romanhujer/SQM/Doc/Android KstartLite.png

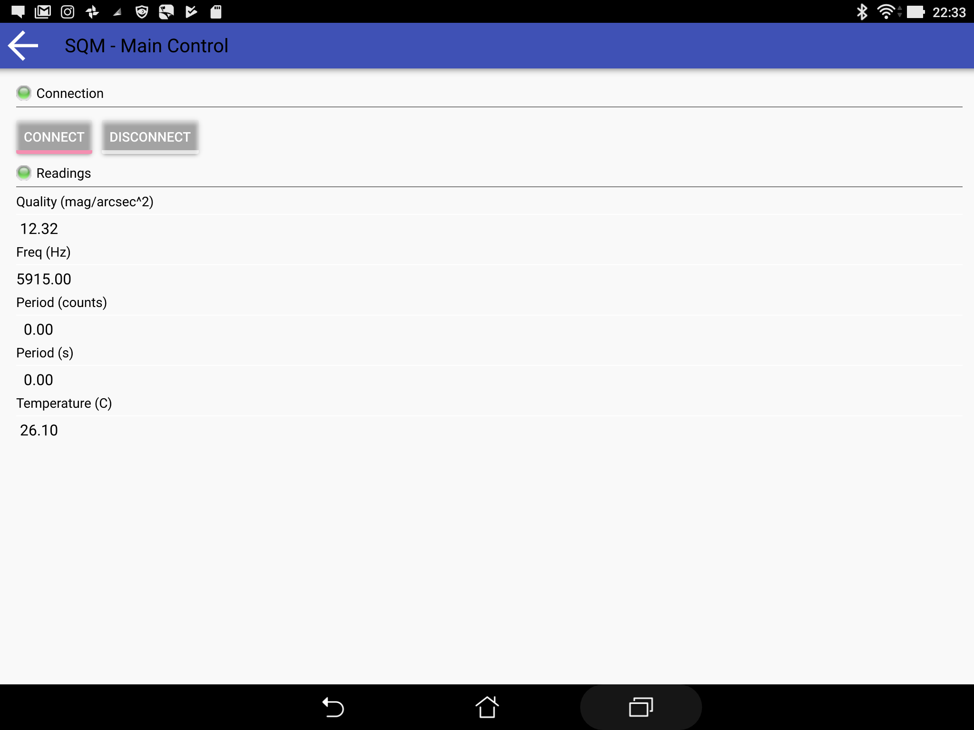
Doc/Android KstartLite.png
