romanhujer/SQM/Doc/Finall version.jpg

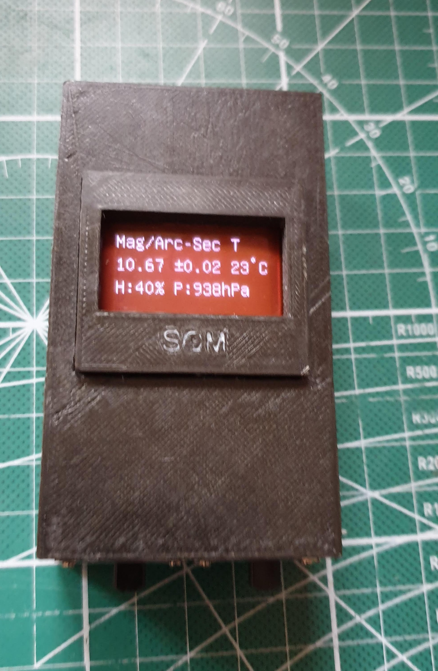
Doc/Finall version.jpg
