romanhujer/SQM/Doc/First prototrype.jpg

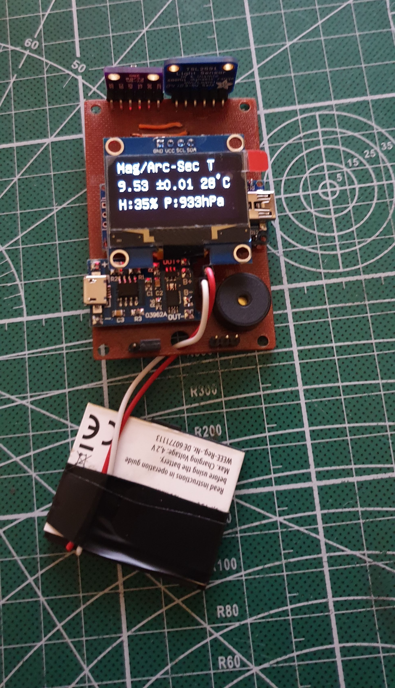
Doc/First prototrype.jpg
