romanhujer/SQM/Doc/Inastall battery.jpg

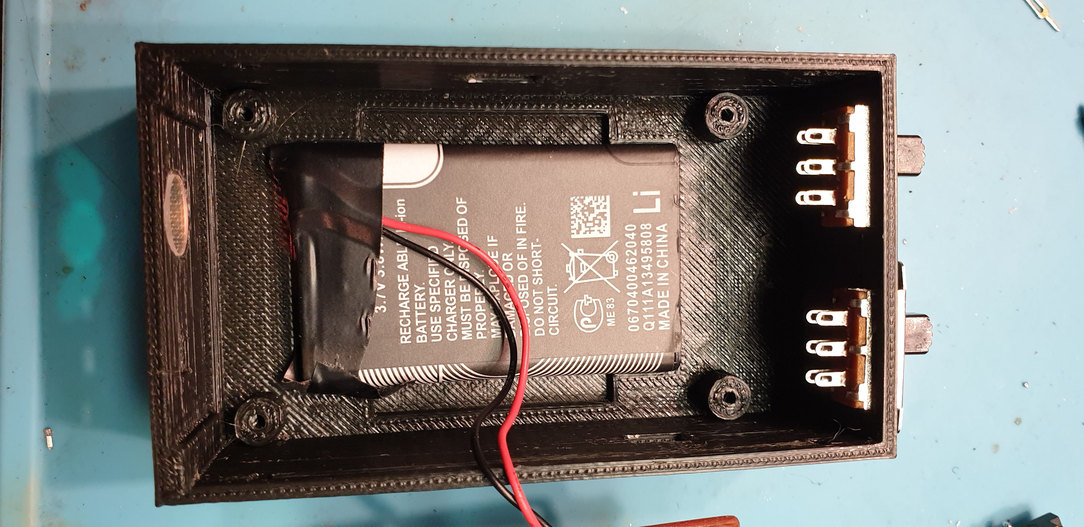
Doc/Inastall battery.jpg
