romanhujer/SQM/Doc/iOS  iINDI.PNG

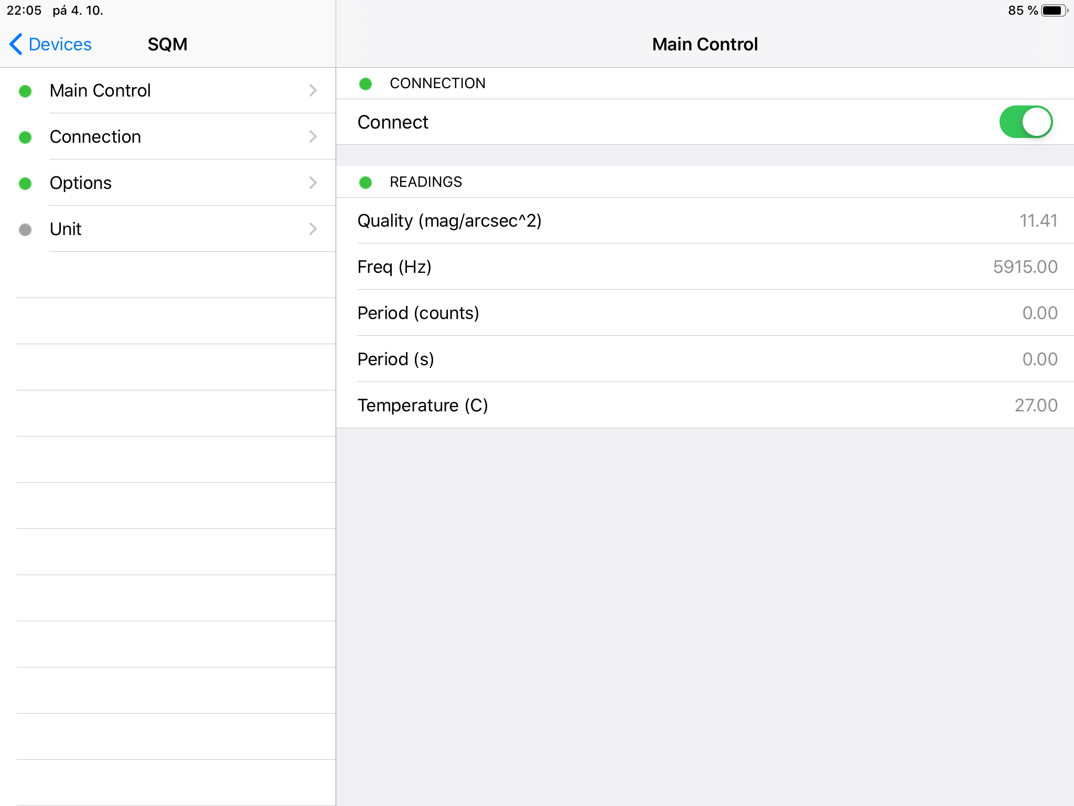
Doc/iOS iINDI.PNG
