romanhujer/SQM/Doc/JLCPCB  profi PCB V1.1b.jpg

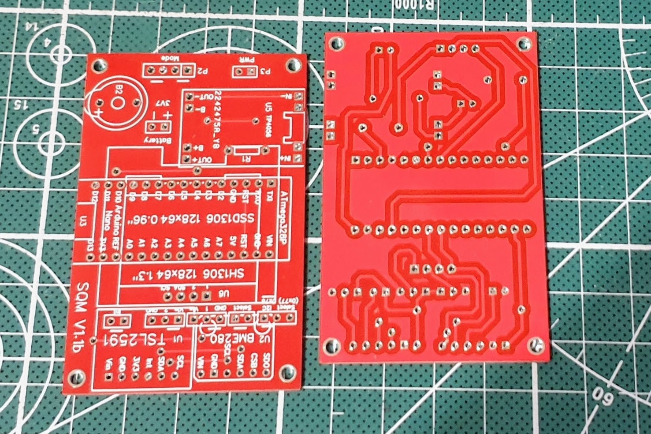
Doc/JLCPCB profi PCB V1.1b.jpg
