romanhujer/SQM/Doc/KStars.png

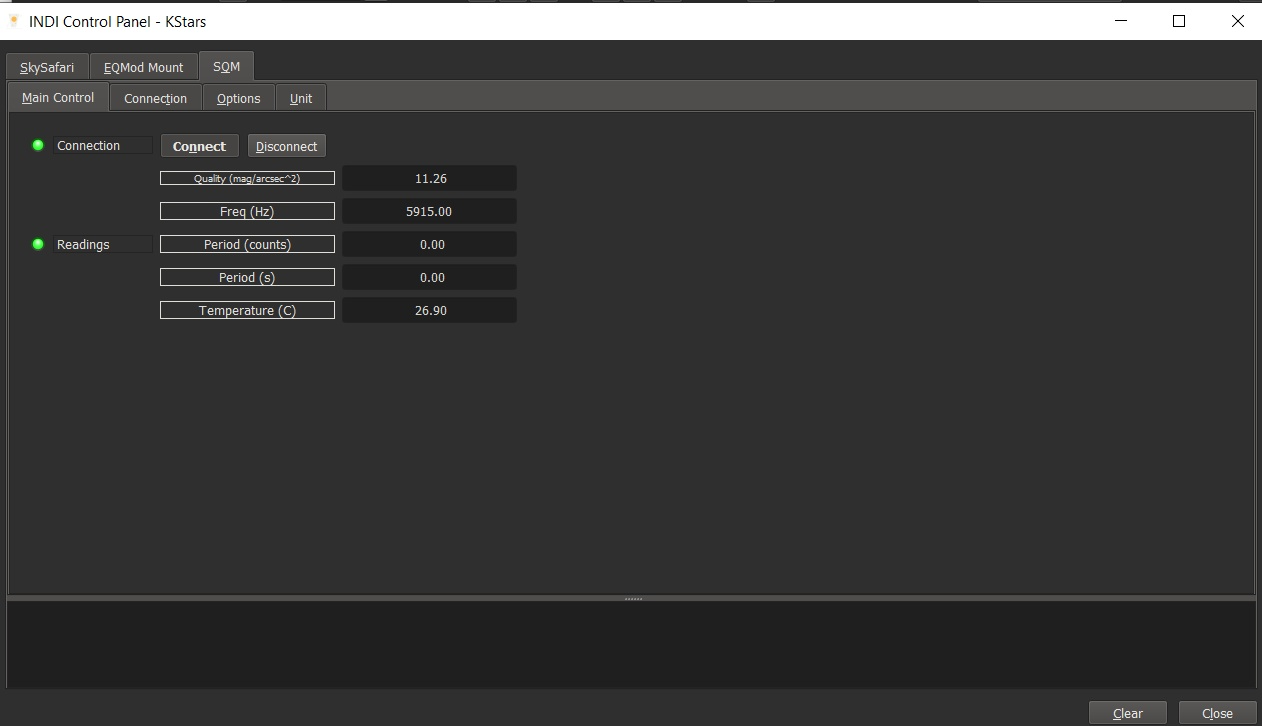
Doc/KStars.png
