romanhujer/SQM/Doc/SQM-in-APT.JPG

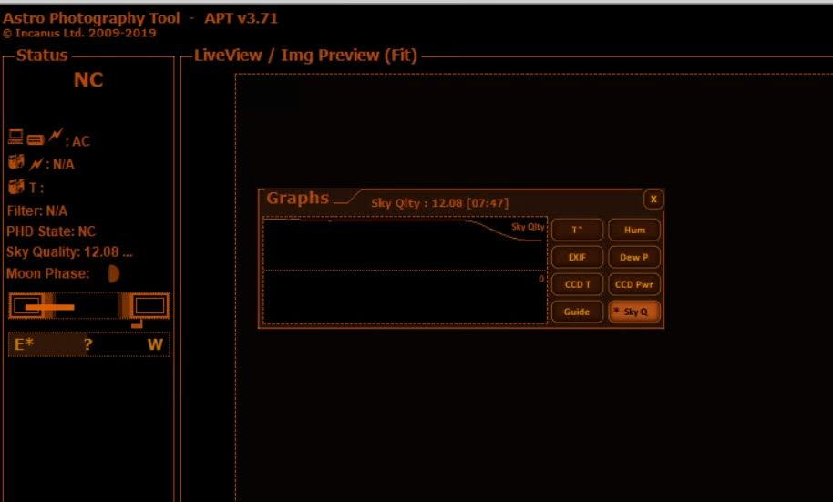
Doc/SQM-in-APT.JPG
