romanhujer/SQM/Doc/SQM.jpg

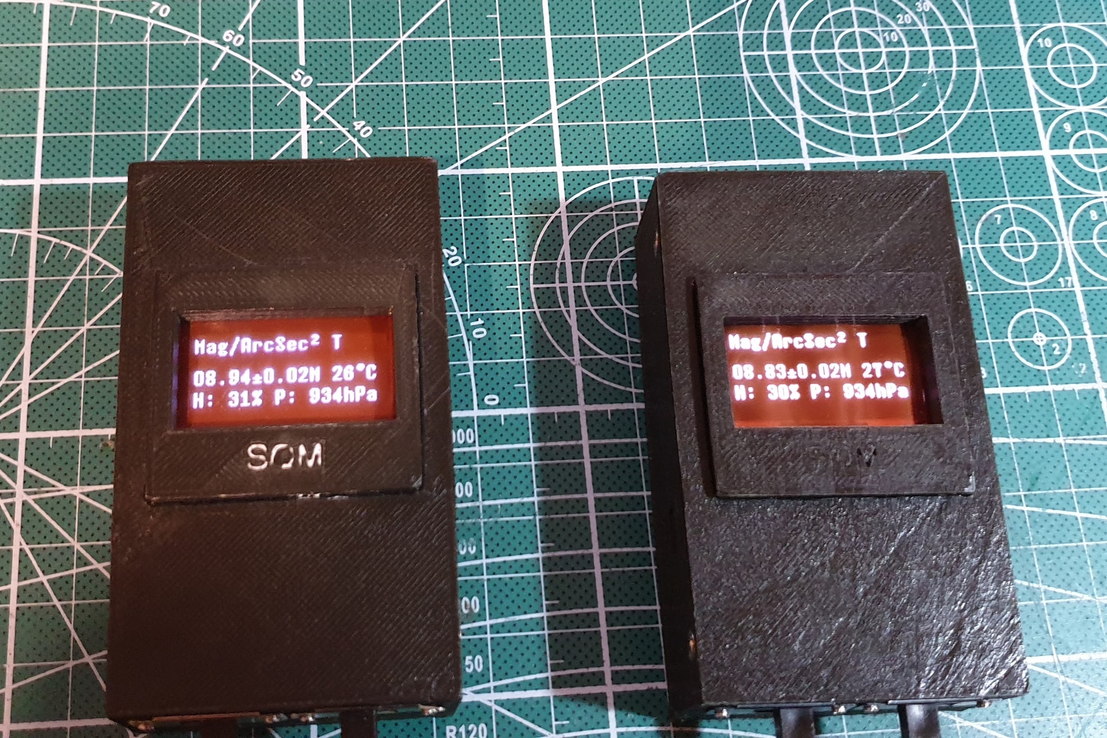
Doc/SQM.jpg
