romanhujer/SQM/Doc/UnihedromApp.JPG

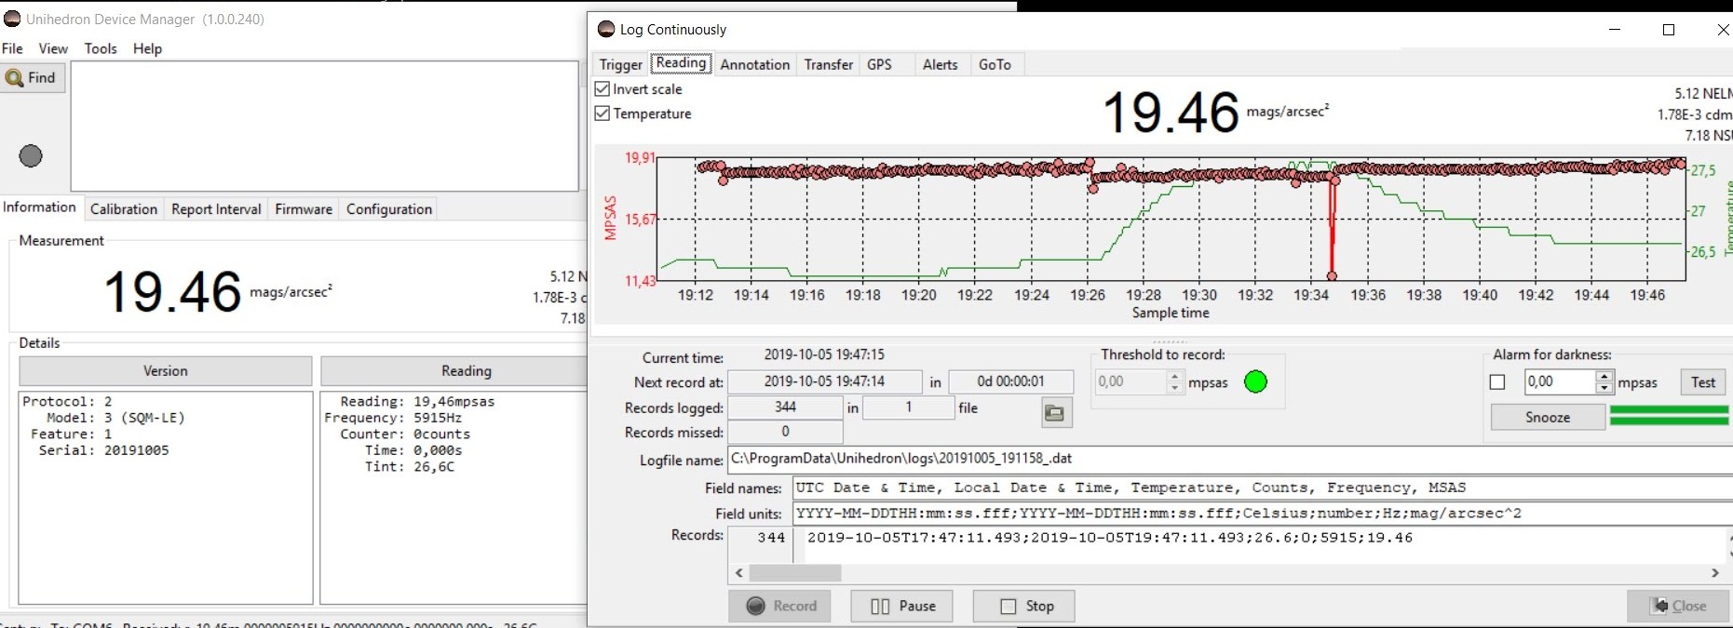
Doc/UnihedromApp.JPG
