romanhujer/SQM/Doc/WebManager BoxInfo.PNG

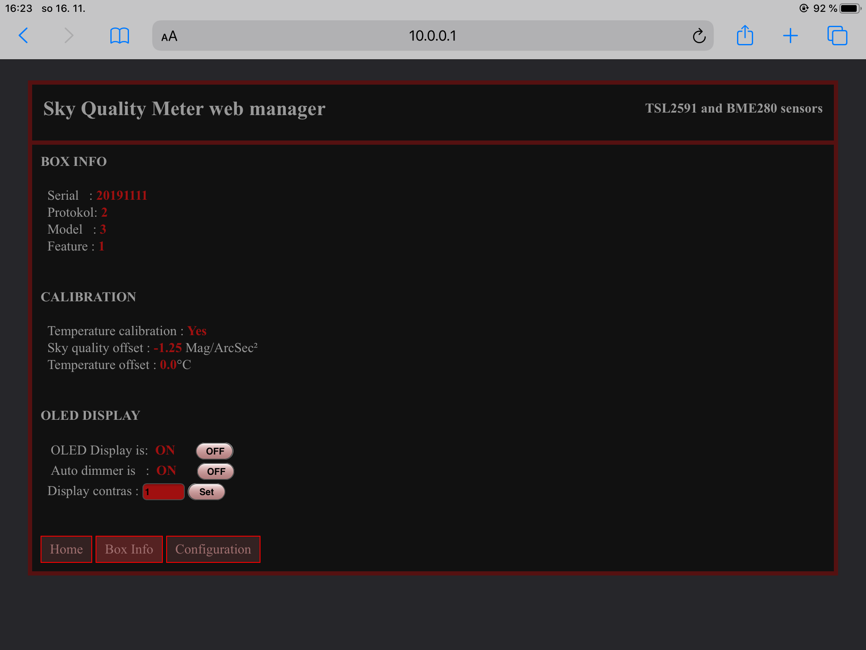
Doc/WebManager BoxInfo.PNG
