romanhujer/SQM/Doc/WebManager Config.PNG

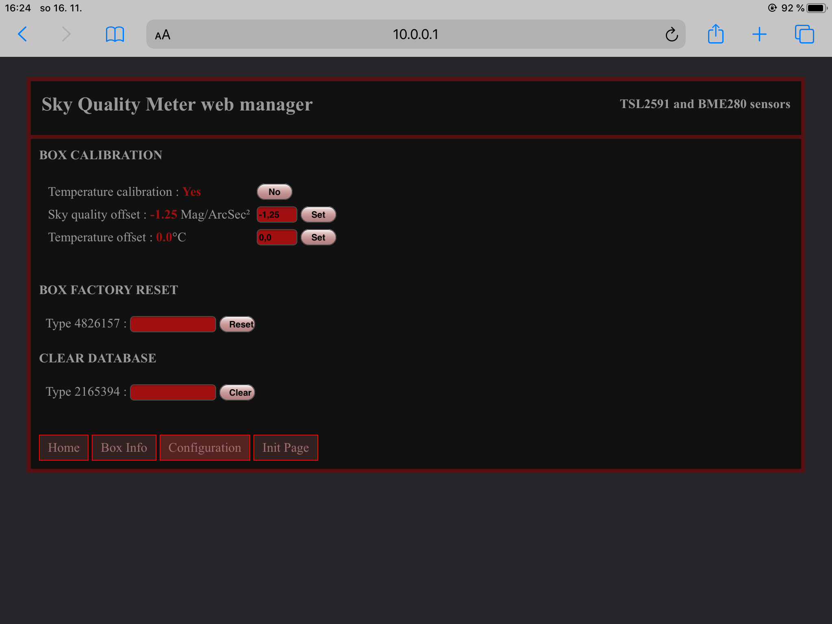
Doc/WebManager Config.PNG
