romanhujer/SQM/Doc/WebManager.PNG

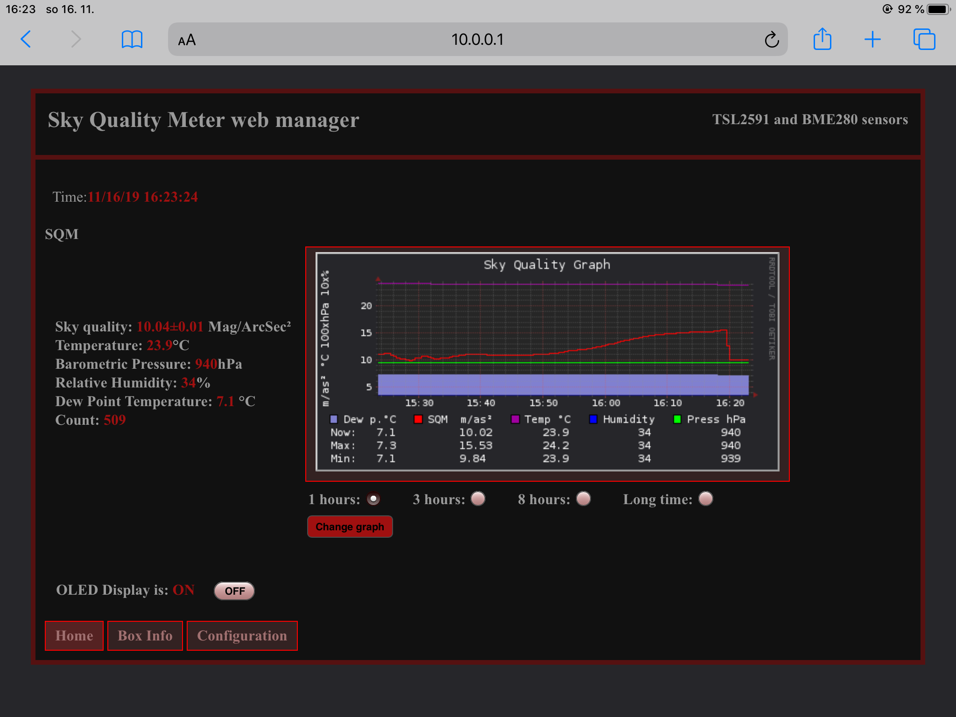
Doc/WebManager.PNG
