romanhujer/SQM/Doc/WebManagerGraphs.PNG

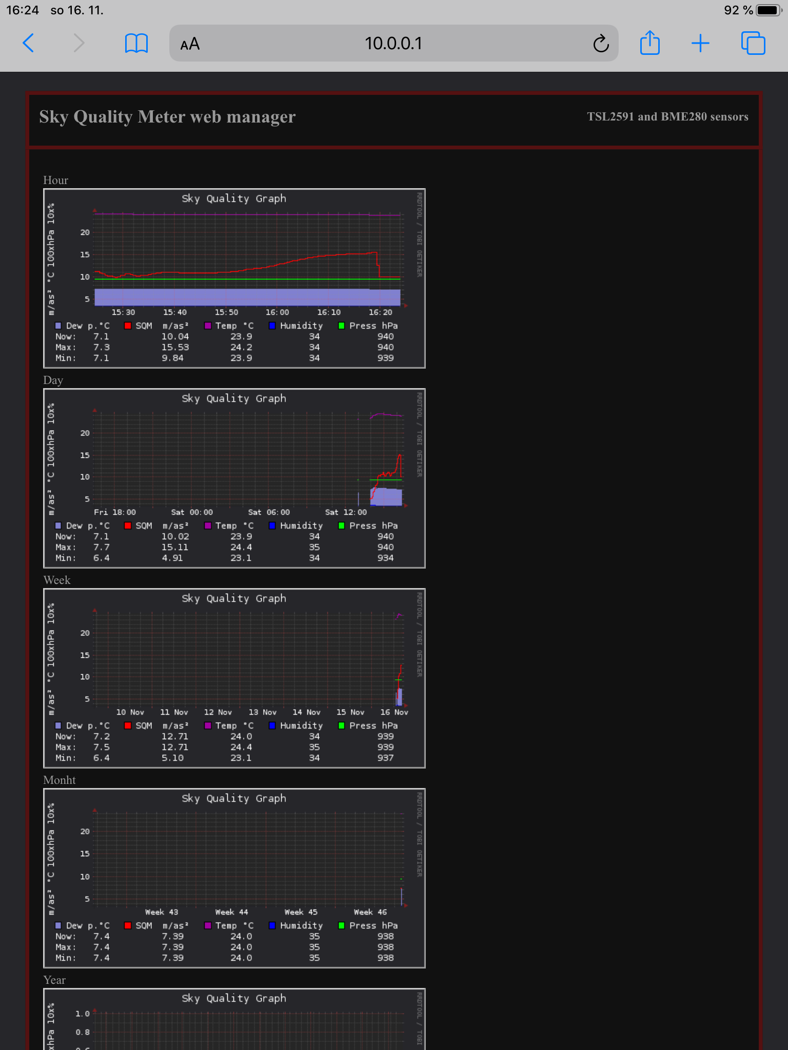
Doc/WebManagerGraphs.PNG
