romanhujer/SQM/sqm.png

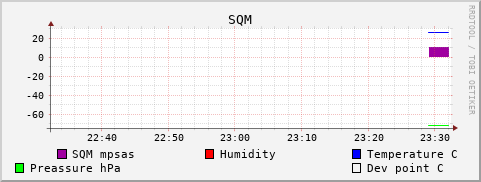
sqm.png
