romanhujer/SQM/sqmrrdweb/views/day.png

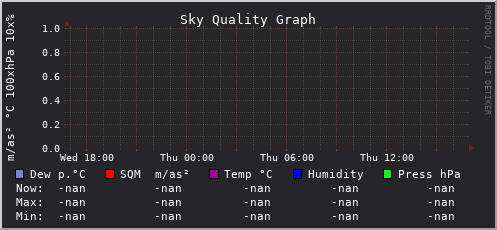
sqmrrdweb/views/day.png
