romanhujer/SQM/sqmrrdweb/views/monht.png

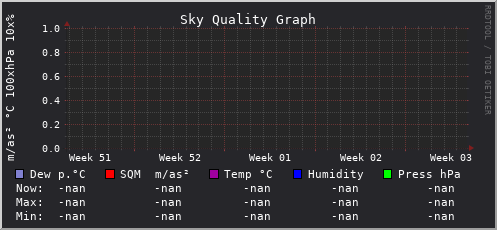
sqmrrdweb/views/monht.png
