romanhujer/SQM/sqmrrdweb/views/sqm.png

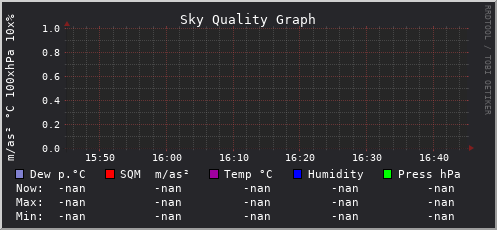
sqmrrdweb/views/sqm.png
