romanhujer/SQM/sqmrrdweb/views/week.png

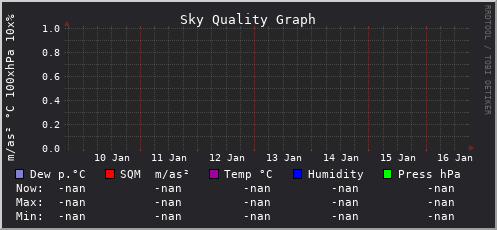
sqmrrdweb/views/week.png
