romanhujer/SQM/sqmrrdweb/views/year.png

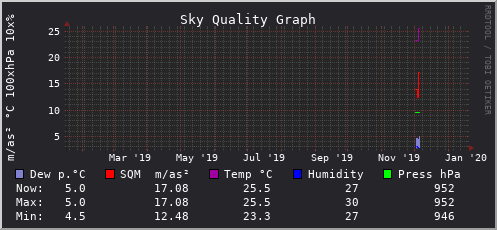
sqmrrdweb/views/year.png
