romanhujer/SQM/3DModelsForCase/stl_nano/SQMBoxT_fixed.stl

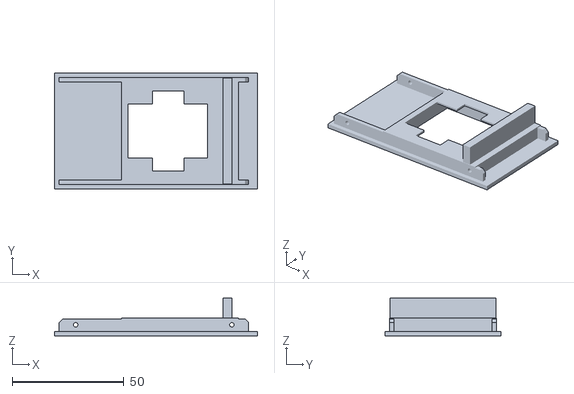
[picture p41: CAD file, 2019-10-04]
3DModelsForCase/stl_nano/SQMBoxT_fixed.stl
91.0 x 52.0 x 17.0
