romanhujer/SQM/3DModelsForCase/ESP-01 SQM.dxf

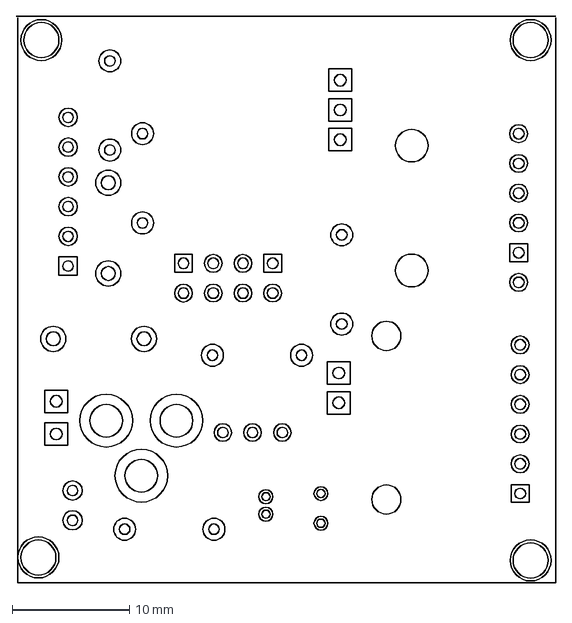
[picture p42: CAD file, 2020-02-24]
3DModelsForCase/ESP-01 SQM.dxf
46.1 x 48.4 mm
