romanhujer/SQM/3DModelsForCase/stl_esp01/ESP-01-SQM-cap_fixed.obj

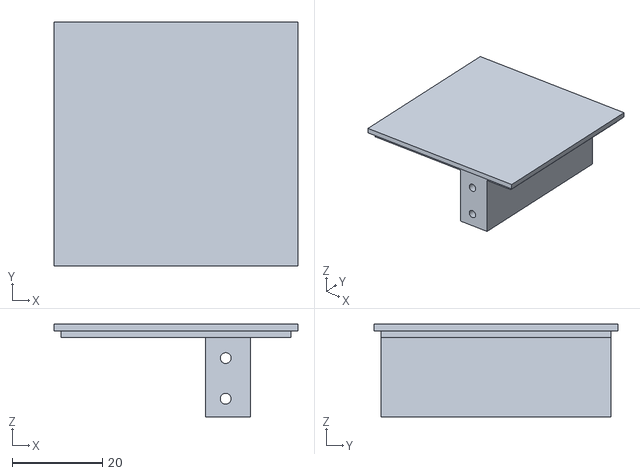
[picture p43: CAD file, 2020-02-24]
3DModelsForCase/stl_esp01/ESP-01-SQM-cap_fixed.obj
54.0 x 54.0 x 20.5
