romanhujer/SQM/3DModelsForCase/stl_nano/SQMFace SH1106_fixed.stl

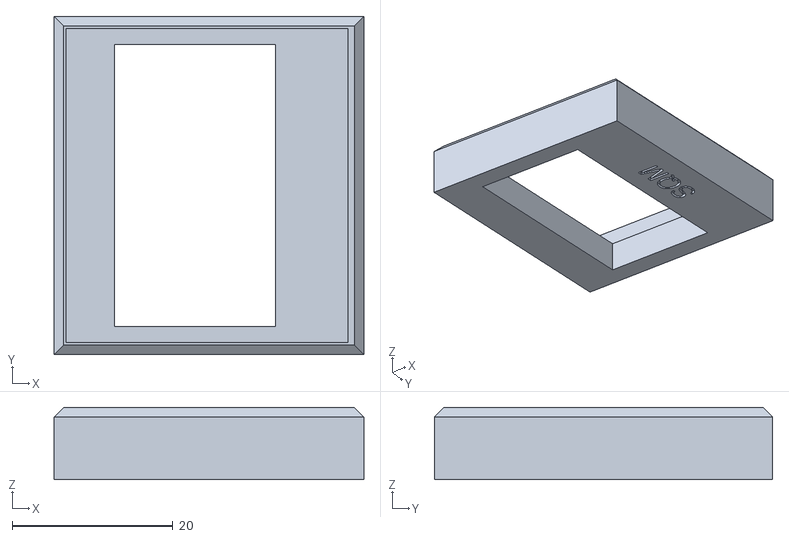
[picture p44: CAD file, 2019-10-04]
3DModelsForCase/stl_nano/SQMFace SH1106_fixed.stl
38.5 x 42.0 x 9.00
