romanhujer/SQM/3DModelsForCase/SQM PCB V1.0.dxf

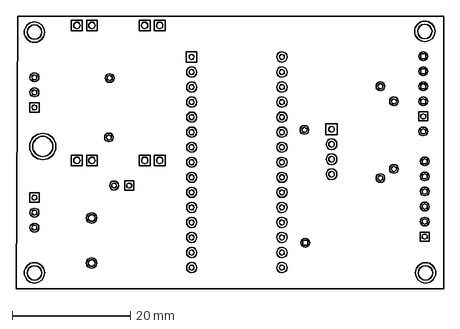
[picture p45: CAD file, 2019-10-01]
3DModelsForCase/SQM PCB V1.0.dxf
72.1 x 46.0 mm
