romanhujer/SQM/3DModelsForCase/stl_esp01/ESP-01-SQM-cover_fixed.obj

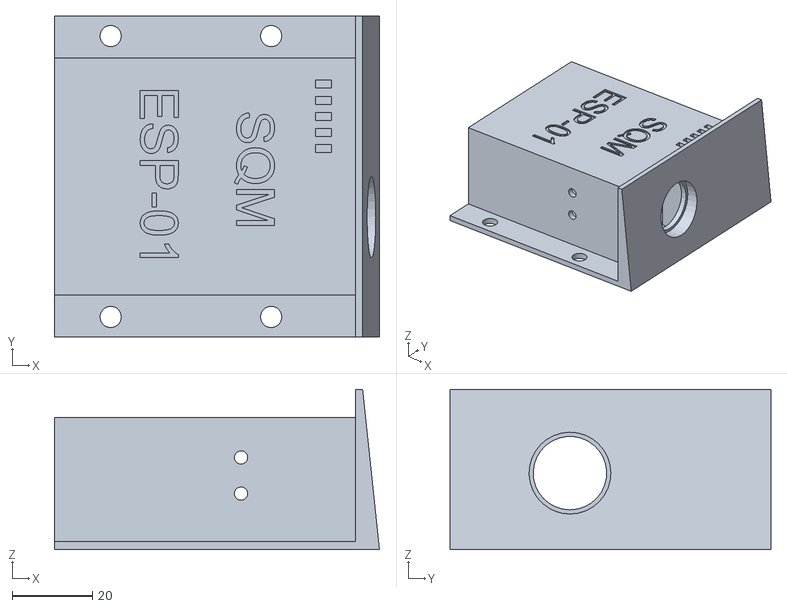
[picture p46: CAD file, 2020-02-24]
3DModelsForCase/stl_esp01/ESP-01-SQM-cover_fixed.obj
81.0 x 80.0 x 40.0
