romanhujer/SQM/3DModelsForCase/stl_esp01/ESP-01-SQM-box_fixed.obj

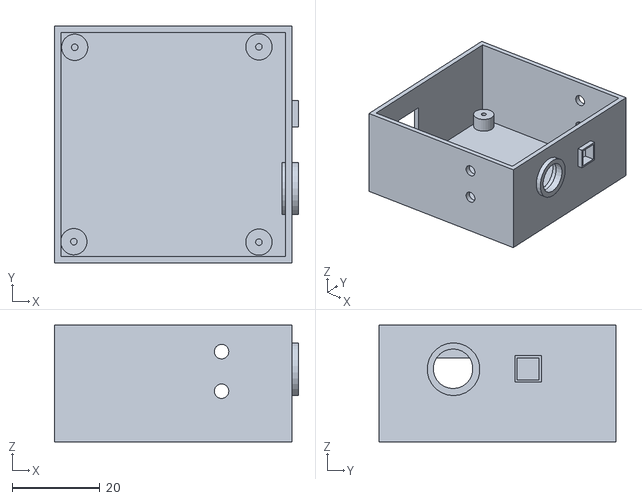
[picture p47: CAD file, 2020-02-24]
3DModelsForCase/stl_esp01/ESP-01-SQM-box_fixed.obj
55.5 x 54.0 x 26.5
