romanhujer/SQM/3DModelsForCase/stl_esp8266/SQM-ESP8266-cover.stl

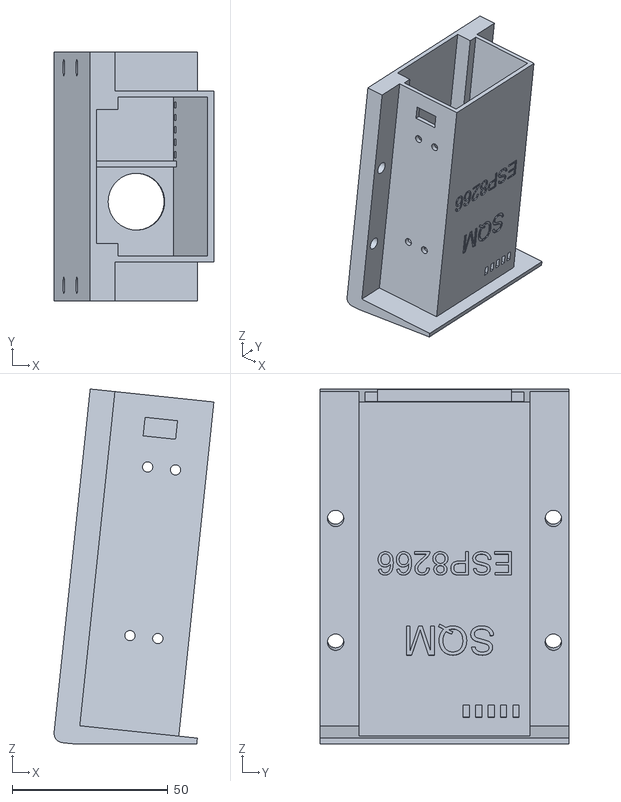
[picture p48: CAD file, 2020-02-26]
3DModelsForCase/stl_esp8266/SQM-ESP8266-cover.stl
51.4 x 80.0 x 114.1
