romanhujer/SQM/3DModelsForCase/stl_esp8266/SQM-ESP8266-cover_fixed.obj

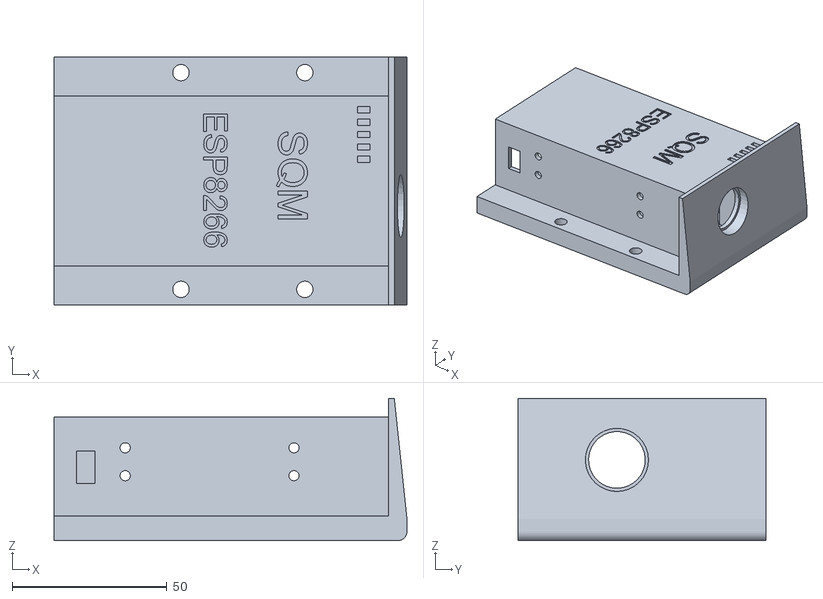
[picture p49: CAD file, 2020-02-26]
3DModelsForCase/stl_esp8266/SQM-ESP8266-cover_fixed.obj
114.0 x 80.0 x 46.0
