romanhujer/SQM/3DModelsForCase/stl_esp8266/SQM-ESP8266-cap_fixed.obj

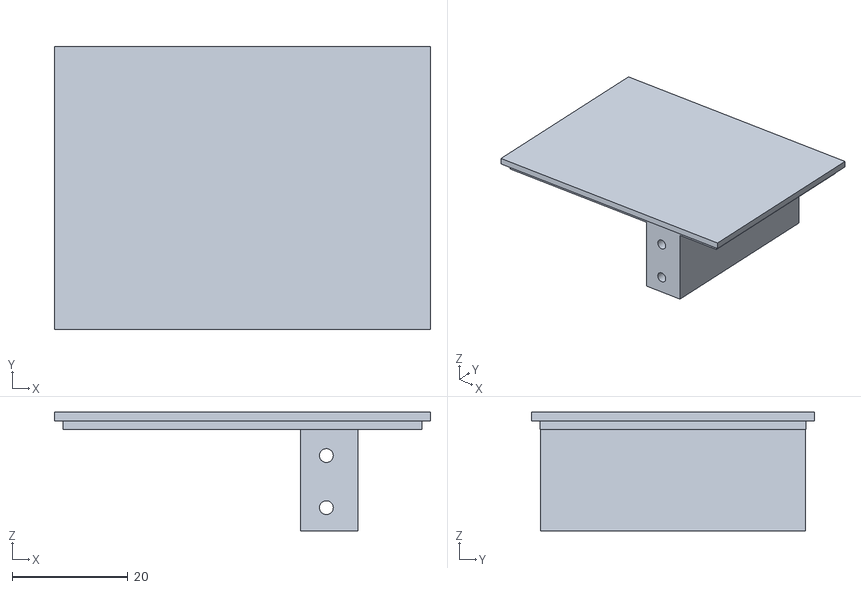
[picture p50: CAD file, 2020-02-25]
3DModelsForCase/stl_esp8266/SQM-ESP8266-cap_fixed.obj
65.0 x 49.0 x 20.5
