romanhujer/SQM/3DModelsForCase/stl_esp8266/SQM-ESP8266-box_fixed.obj

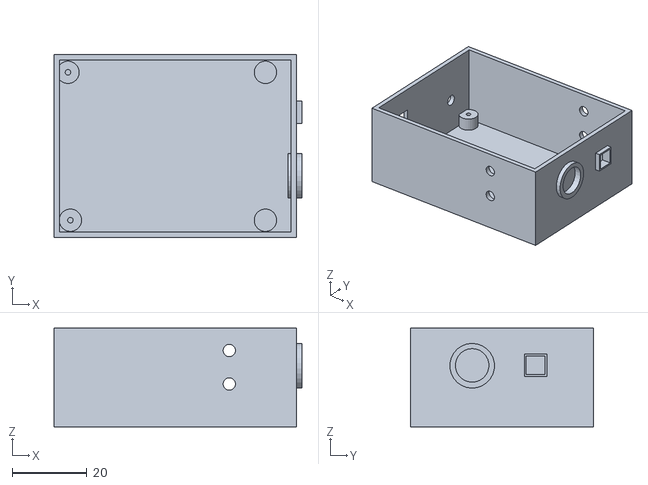
[picture p51: CAD file, 2020-02-25]
3DModelsForCase/stl_esp8266/SQM-ESP8266-box_fixed.obj
66.5 x 49.0 x 26.5
